cr1901/AT2XT/src/peripheral.rs

use msp430::interrupt::{CriticalSection, Mutex};
use once_cell::unsync::OnceCell;

static PERIPHERALS: Mutex<OnceCell<At2XtPeripherals>> = Mutex::new(OnceCell::new());

pub struct At2XtPeripherals {
    pub port: msp430g2211::PORT_1_2,
    pub timer: msp430g2211::TIMER_A2,
}

impl AsRef<msp430g2211::PORT_1_2> for At2XtPeripherals {
    fn as_ref(&self) -> &msp430g2211::PORT_1_2 {
        &self.port
    }
}

impl AsRef<msp430g2211::TIMER_A2> for At2XtPeripherals {
    fn as_ref(&self) -> &msp430g2211::TIMER_A2 {
        &self.timer
    }
}

impl At2XtPeripherals {
    pub fn init<'a>(self, cs: CriticalSection<'a>) -> Result<(), ()> {
        // We want to consume our Peripherals struct so interrupts
        // and the main thread can access the peripherals; OnceCell
        // returns the data to you on error.
        PERIPHERALS.borrow(cs).set(self).map_err(|_e| {})
    }

    pub fn periph_ref<'a, T>(cs: CriticalSection<'a>) -> Option<&'a T>
    where
        Self: AsRef<T>,
    {
        PERIPHERALS.borrow(cs).get().map(|p| p.as_ref())
    }
}
